Picatout/pomme_1P/KiCAD/pomme-1+/alimentation.kicad_sch

## KiCad design KiCAD/pomme-1+/alimentation.kicad_sch (2025-05-06, an earlier design)

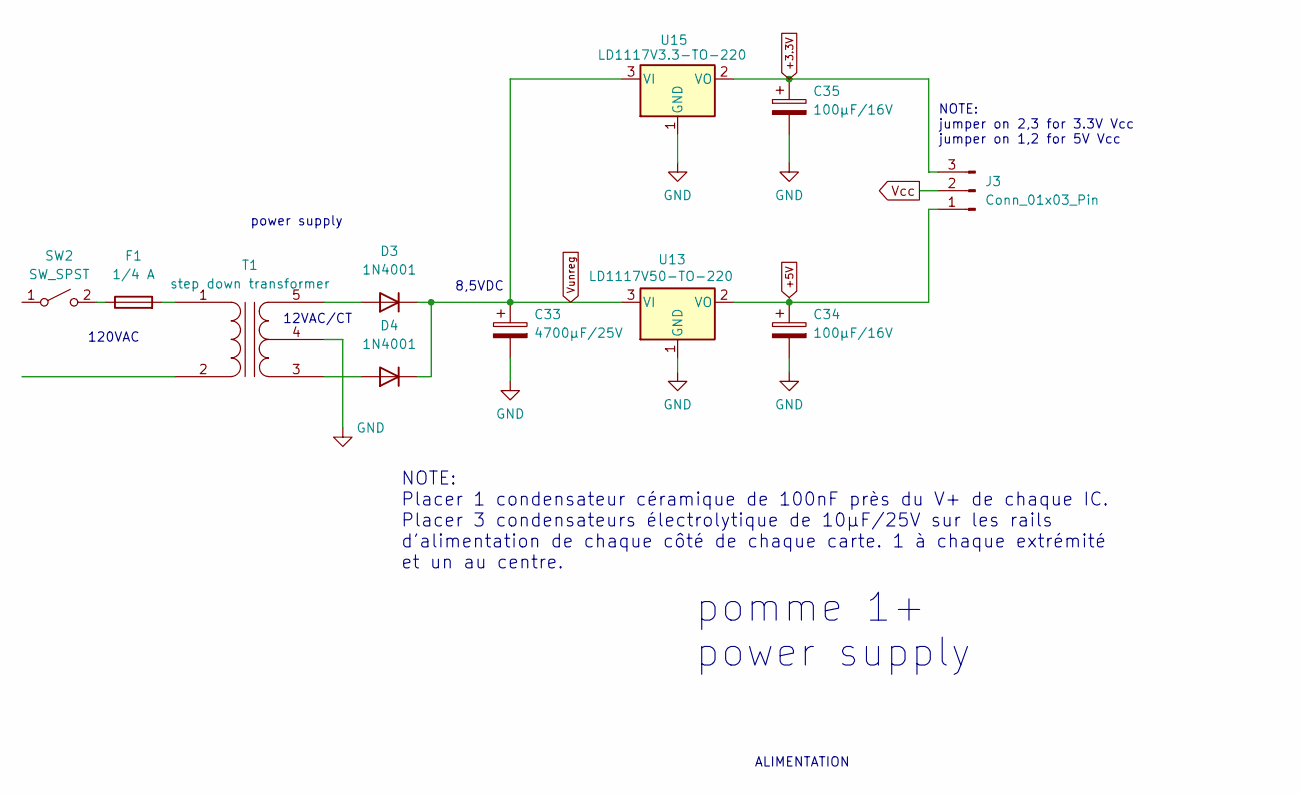
[picture p36: schematic alimentation.kicad_sch]

Parts:
C33: 4700µF/25V
C34, C35: 100µF/16V
D3, D4: 1N4001; D_DO-41_SOD81_P10.16mm_Horizontal
F1: 1/4 A
J3: Conn_01x03_Pin
SW2: SW_SPST
T1: step down transformer
U13: LD1117V50-TO-220; SOT-223-3_TabPin2
U15: LD1117V3.3-TO-220; SOT-223-3_TabPin2

Connections:
+3.3V: C35.1, J3.3, U15.2 (VO)
+5V: C34.1, J3.1, U13.2 (VO)
GND: C33.2, C34.2, C35.2, T1.4 (SC), U13.1 (GND), U15.1 (GND)
unnamed: D3.2 (A), T1.5 (SB)
unnamed: D4.2 (A), T1.3 (SA)
unnamed: F1.1, SW2.2 (B)
unnamed: F1.2, T1.1 (AA)
Vcc: J3.2
Vunreg: C33.1, D3.1 (K), D4.1 (K), U13.3 (VI), U15.3 (VI)

Notes on the sheet:
NOTE: jumper on 2,3 for 3.3V Vcc jumper on 1,2 for 5V Vcc
120VAC
NOTE: Placer 1 condensateur céramique de 100nF près du V+ de chaque IC. Placer 3 condensateurs électrolytique de 10µF/25V sur les rails d'alimentation de chaque côté de chaque carte. 1 à chaque extrémité et un au centre.
pomme 1+ power supply
power supply
12VAC/CT
8,5VDC
ALIMENTATION
