Picatout/pomme_1P/KiCAD/pomme-1+/drive.kicad_sch

## KiCad design KiCAD/pomme-1+/drive.kicad_sch (2025-03-16)

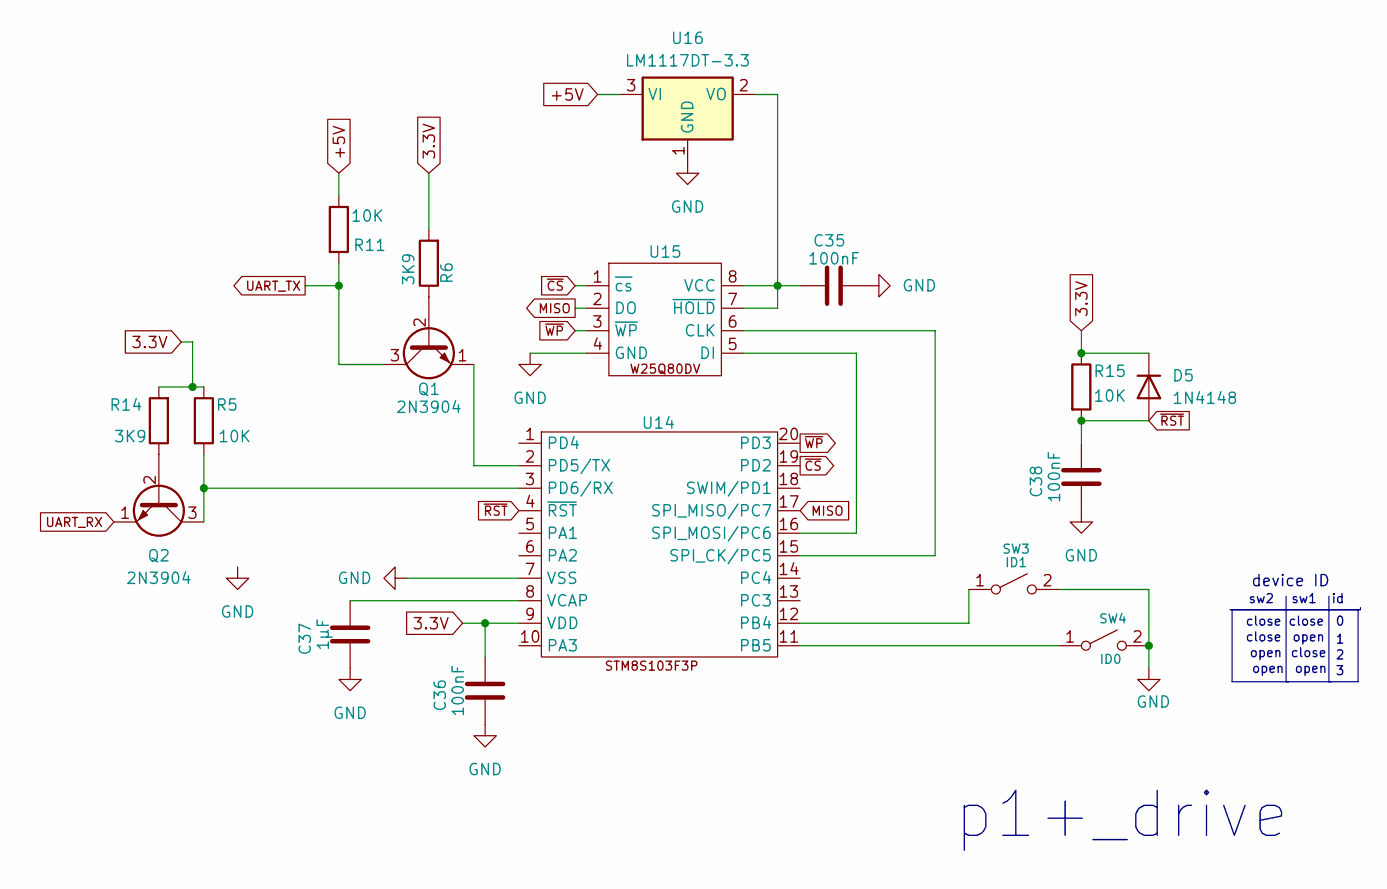
[picture p37: schematic drive.kicad_sch]

Parts:
C35, C36, C38: 100nF
C37: 1µF
D5: 1N4148; D_DO-35_SOD27_P7.62mm_Horizontal
Q1, Q2: 2N3904; TO-92_Inline
R5, R11, R15: 10K
R6, R14: 3K9
SW3: ID1
SW4: ID0
U14, U15: (no value)
U16: LM1117DT-3.3; TO-252-3_TabPin2

Connections:
3.3V: C36.2, D5.1 (K), R5.1, R6.2, R14.2, R15.1, U14.9 (VDD)
+5V: R11.1, U16.3 (VI)
GND: C35.2, C36.1, C37.1, C38.1, SW3.2 (B), SW4.2 (B), U14.7 (VSS), U15.4 (GND), U16.1 (GND)
MISO: U14.17 (SPI_MISO/PC7), U15.2 (DO)
unnamed: C35.1, U15.7 (~HOLD), U15.8 (VCC), U16.2 (VO)
unnamed: C37.2, U14.8 (VCAP)
unnamed: Q1.1 (E), U14.2 (PD5/TX)
unnamed: Q1.2 (B), R6.1
unnamed: Q2.2 (B), R14.1
unnamed: Q2.3 (C), R5.2, U14.3 (PD6/RX)
unnamed: SW3.1 (A), U14.12 (PB4)
unnamed: SW4.1 (A), U14.11 (PB5)
unnamed: U14.15 (SPI_CK/PC5), U15.6 (CLK)
unnamed: U14.16 (SPI_MOSI/PC6), U15.5 (DI)
UART_RX: Q2.1 (E)
UART_TX: Q1.3 (C), R11.2
~CS: U14.19 (PD2), U15.1 (~cs)
~RST: C38.2, D5.2 (A), R15.2, U14.4 (~RST)
~WP: U14.20 (PD3), U15.3 (~WP)

Notes on the sheet:
close
sw1
open
device ID
sw2
p1+_drive
