Picatout/pomme_1P/KiCAD/pomme-1+/mémoire.kicad_sch

## KiCad design KiCAD/pomme-1+/mémoire.kicad_sch (2025-06-10, an earlier design)

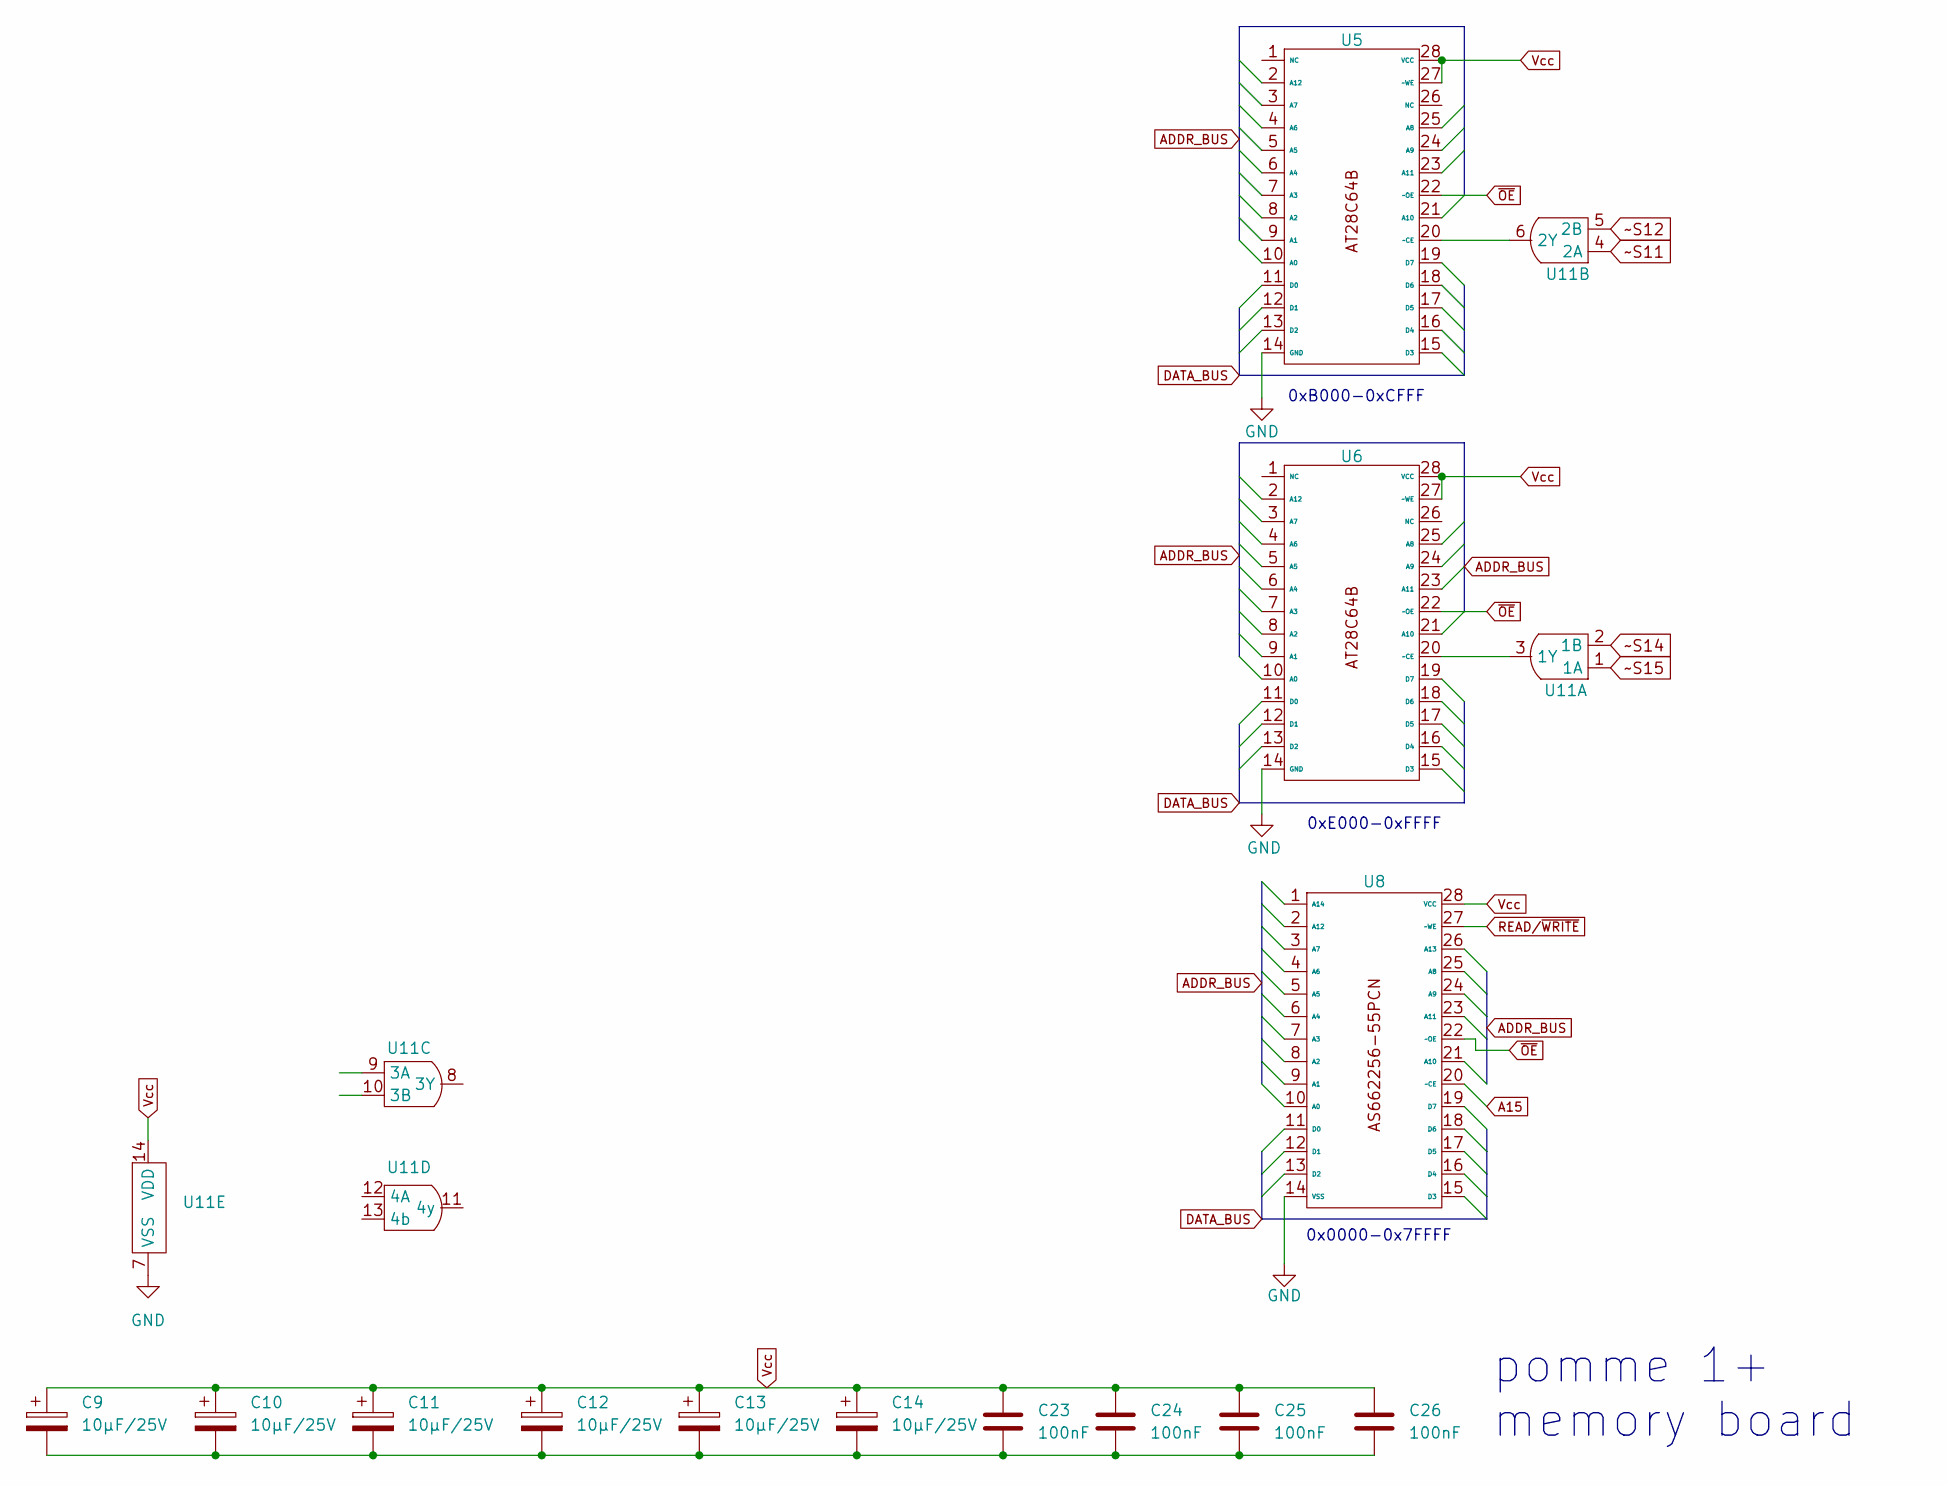
[picture p38: schematic mémoire.kicad_sch]

Parts:
C9, C10, C11, C12, C13, C14: 10µF/25V
C23, C24, C25, C26: 100nF
U5, U6, U8, U11: (no value)

Connections:
GND: U5.14 (GND), U6.14 (GND), U8.14 (VSS), U11.7 (VSS)
unnamed: C9.2, C10.2, C11.2, C12.2, C13.2, C14.2, C23.2, C24.2, C25.2, C26.2
unnamed: U6.20 (~CE), U11.3 (1Y)
unnamed: U5.20 (~CE), U11.6 (2Y)
READ/~WRITE: U8.27 (~WE)
Vcc: C9.1, C10.1, C11.1, C12.1, C13.1, C14.1, C23.1, C24.1, C25.1, C26.1, U5.27 (~WE), U5.28 (VCC), U6.27 (~WE), U6.28 (VCC), U8.28 (VCC), U11.14 (VDD)
~S11: U11.4 (2A)
~S12: U11.5 (2B)
~S14: U11.2 (1B)
~S15: U11.1 (1A)
~OE: U5.22 (~OE), U6.22 (~OE), U8.22 (~OE)

Notes on the sheet:
0x0000-0x7FFFF
0xB000-0xCFFF
pomme 1+ memory board
0xE000-0xFFFF
