Picatout/pomme_1P/KiCAD/pomme-1+/pomme-1.5.kicad_sch

## KiCad design KiCAD/pomme-1+/pomme-1.5.kicad_sch (2025-06-10, an earlier design)

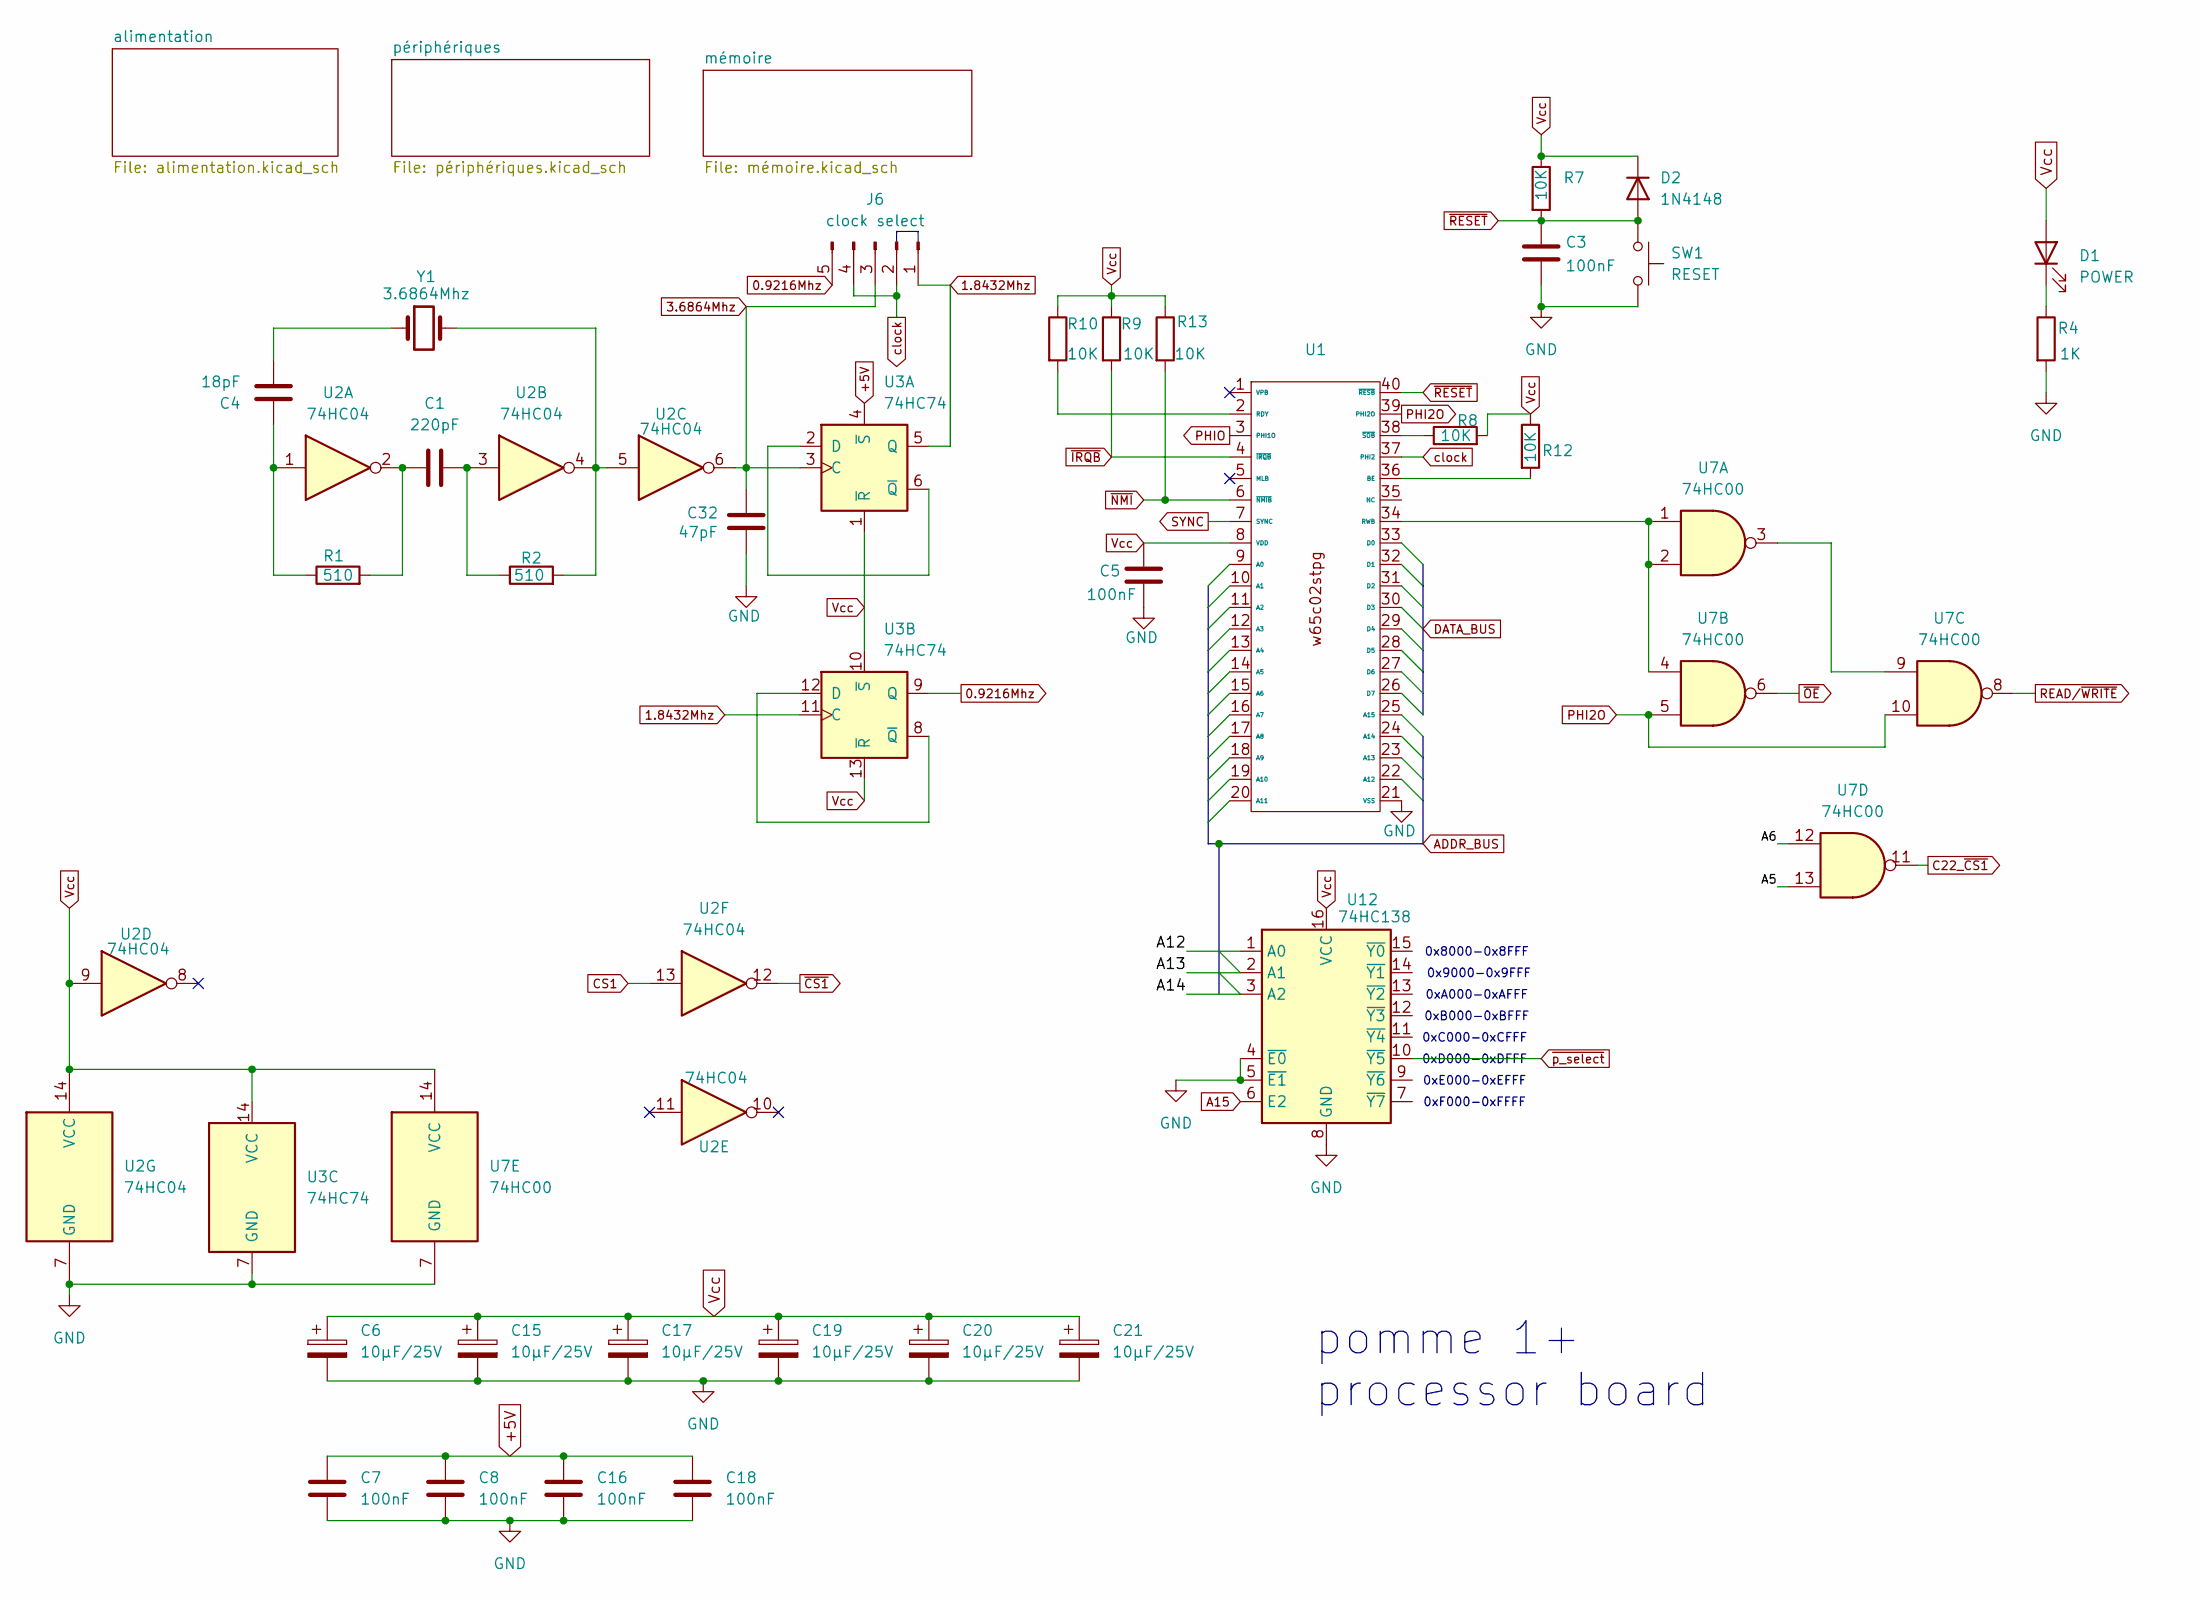
[picture p39: schematic pomme-1.5.kicad_sch]

Parts:
C1: 220pF
C3, C5, C7, C8, C16, C18: 100nF
C4: 18pF
C6, C15, C17, C19, C20, C21: 10µF/25V
C32: 47pF
D1: POWER
D2: 1N4148; D_DO-35_SOD27_P7.62mm_Horizontal
J6: clock select
R1, R2: 510
R4: 1K
R7, R8, R9, R10, R12, R13: 10K
SW1: RESET
U1: (no value)
U2: 74HC04
U3: 74HC74
U7: 74HC00
U12: 74HC138
Y1: 3.6864Mhz

Connections:
0.9216Mhz: J6.5, U3.9 (Q)
1.8432Mhz: J6.1, U3.5 (Q), U3.11 (C)
3.6864Mhz: C32.2, J6.3, U2.6, U3.3 (C)
+5V: C7.1, C8.1, C16.1, C18.1, U3.4 (~S)
A5: U7.13
A6: U7.12
A12: U12.1 (A0)
A13: U12.2 (A1)
A14: U12.3 (A2)
A15: U12.6 (E2)
C22_~CS1: U7.11
CS1: U2.13
GND: C3.2, C5.2, C6.2, C7.2, C8.2, C15.2, C16.2, C17.2, C18.2, C19.2, C20.2, C21.2, C32.1, R4.2, SW1.3 (B), SW1.4 (B), U1.21 (VSS), U2.7 (GND), U3.7 (GND), U7.7 (GND), U12.4 (~E0), U12.5 (~E1), U12.8 (GND)
unnamed: C1.1, R1.2, U2.2
unnamed: C1.2, R2.1, U2.3
unnamed: C4.1, Y1.1
unnamed: C4.2, R1.1, U2.1
unnamed: D1.1 (K), R4.1
unnamed: R2.2, U2.4, U2.5, Y1.2
unnamed: R8.1, U1.38 (~SOB)
unnamed: R10.2, U1.2 (RDY)
unnamed: R12.2, U1.36 (BE)
unnamed: U1.34 (RWB), U7.1, U7.2, U7.4
unnamed: U3.2 (D), U3.6 (~Q)
unnamed: U3.8 (~Q), U3.12 (D)
unnamed: U7.3, U7.9
PHI2O: U1.39 (PHI2O), U7.5, U7.10
PHIO: U1.3 (PHI1O)
READ/~WRITE: U7.8
SYNC: U1.7 (SYNC)
Vcc: C5.1, C6.1, C15.1, C17.1, C19.1, C20.1, C21.1, D1.2 (A), D2.1 (K), R7.1, R8.2, R9.1, R10.1, R12.1, R13.1, U1.8 (VDD), U2.9, U2.14 (VCC), U3.1 (~R), U3.10 (~S), U3.13 (~R), U3.14 (VCC), U7.14 (VCC), U12.16 (VCC)
clock: J6.2, J6.4, U1.37 (PHI2)
~CS1: U2.12
~IRQB: R9.2, U1.4 (~IRQB)
~NMI: R13.2, U1.6 (~NMIB)
~OE: U7.6
~RESET: C3.1, D2.2 (A), R7.2, SW1.1 (A), SW1.2 (A), U1.40 (~RESB)
~p_select: U12.10 (~Y5)

Notes on the sheet:
0x9000-0x9FFF
pomme 1+ processor board
0xF000-0xFFFF
0xE000-0xEFFF
0xD000-0xDFFF
0xA000-0xAFFF
0xB000-0xBFFF
0x8000-0x8FFF
0xC000-0xCFFF
