Picatout/pomme_1P/KiCAD/pomme-1+/périphériques.kicad_sch

## KiCad design KiCAD/pomme-1+/périphériques.kicad_sch (2025-06-10, an earlier design)

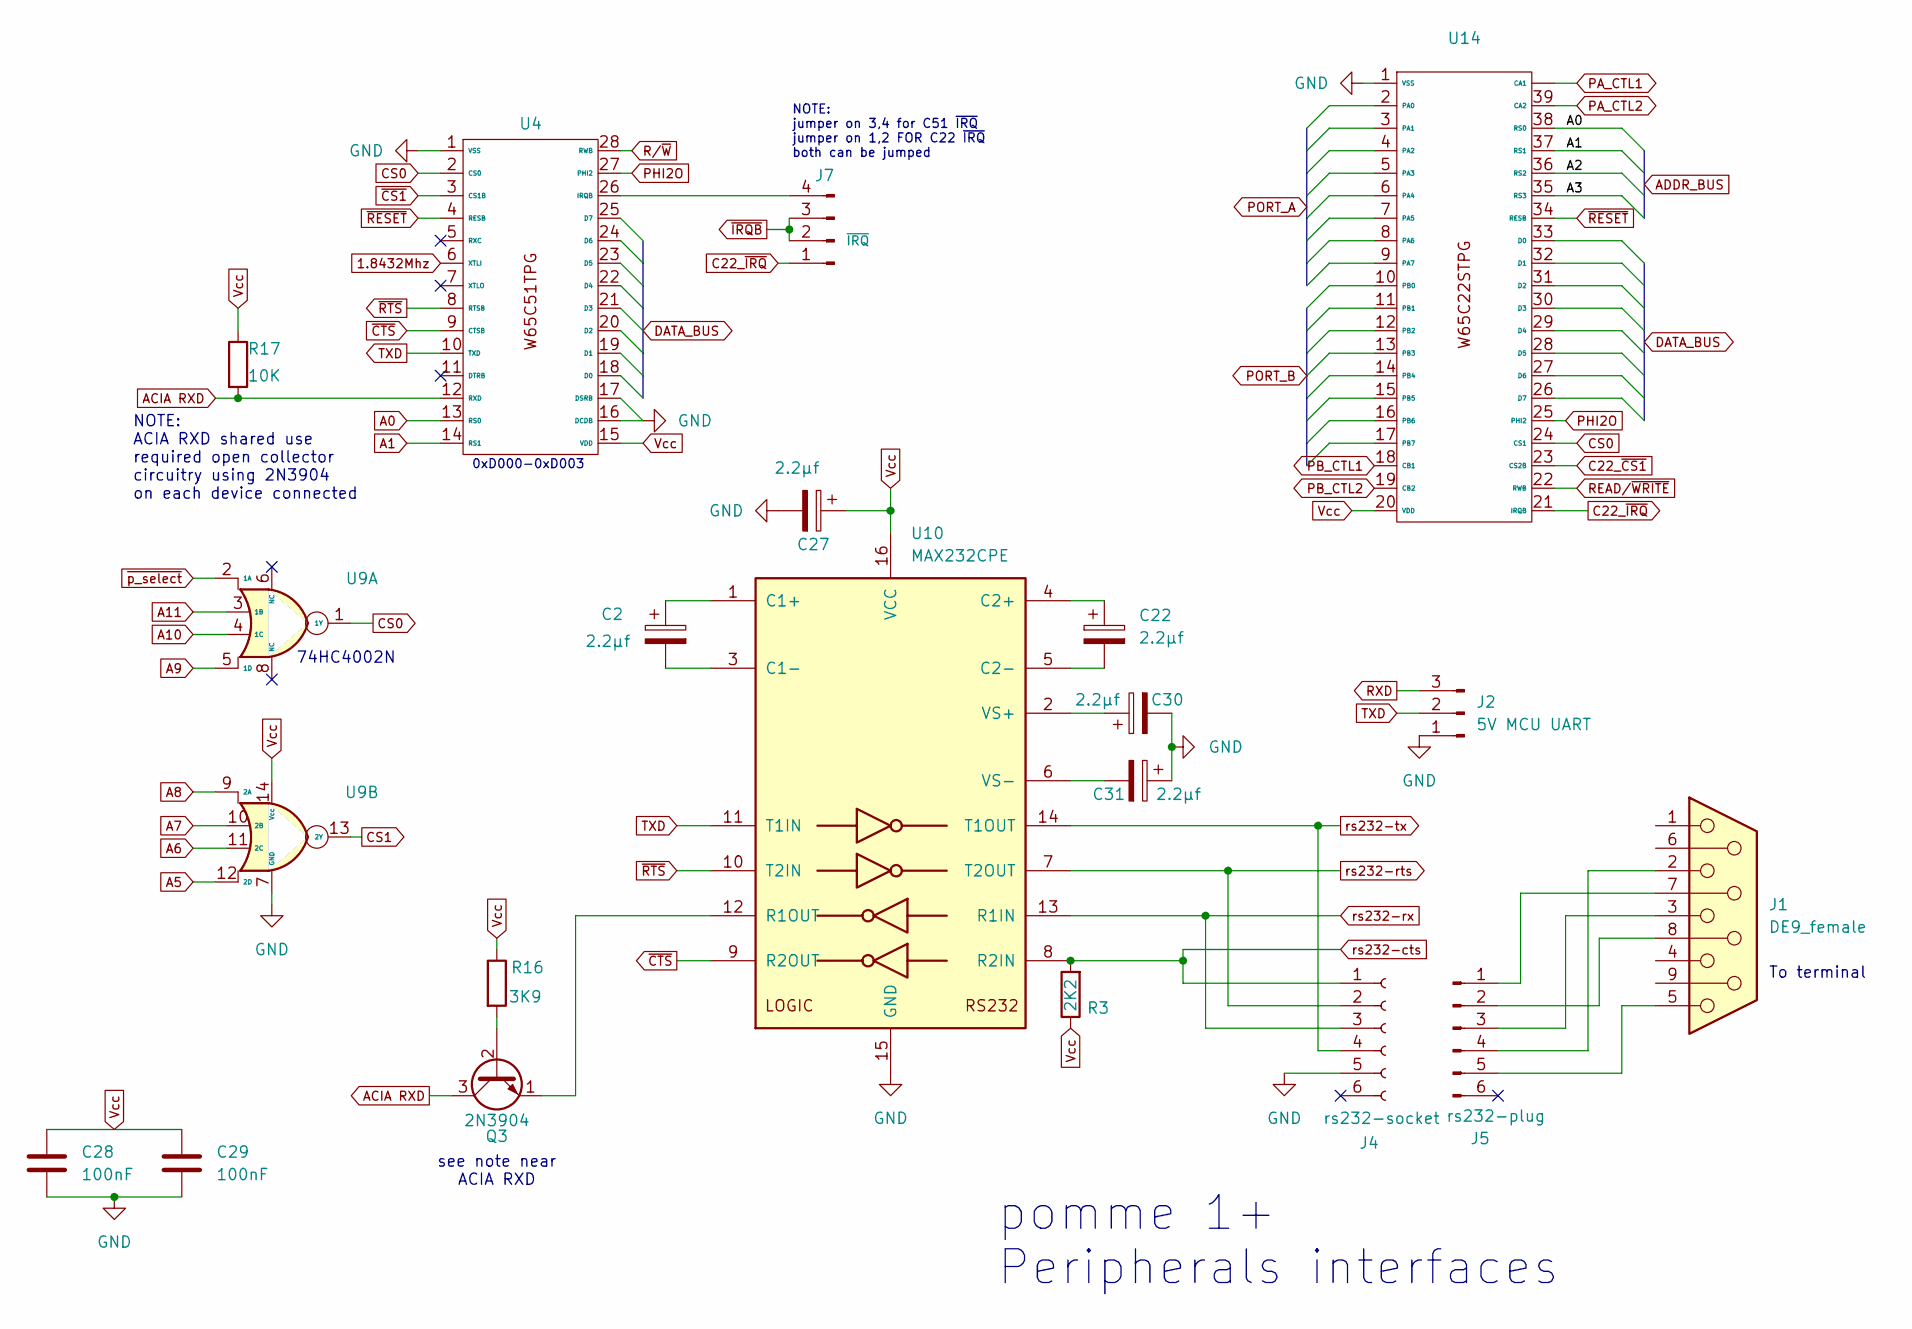
[picture p40: schematic périphériques.kicad_sch]

Parts:
C2, C22, C27, C30, C31: 2.2µf
C28, C29: 100nF
J1: DE9_female
J2: 5V MCU UART
J4: rs232-socket
J5: rs232-plug
J7: ~{IRQ}
Q3: 2N3904; TO-92_Inline
R3: 2K2
R16: 3K9
R17: 10K
U4, U9, U14: (no value)
U10: MAX232CPE

Connections:
1.8432Mhz: U4.6 (XTLI)
A0: U4.13 (RS0), U14.38 (RS0)
A1: U4.14 (RS1), U14.37 (RS1)
A2: U14.36 (RS2)
A3: U14.35 (RS3)
A5: U9.12 (2D)
A6: U9.11 (2C)
A7: U9.10 (2B)
A8: U9.9 (2A)
A9: U9.5 (1D)
A10: U9.4 (1C)
A11: U9.3 (1B)
ACIA RXD: Q3.3 (C), R17.2, U4.12 (RXD)
C22_~CS1: U14.23 (CS2B)
C22_~IRQ: J7.1, U14.21 (IRQB)
CS0: U4.2 (CS0), U9.1 (1Y), U14.24 (CS1)
CS1: U9.13 (2Y)
GND: C27.2, C28.1, C29.2, C30.2, C31.1, J2.1, J4.5, U4.1 (VSS), U4.16 (DCDB), U9.7 (GND), U10.15 (GND), U14.1 (VSS)
unnamed: C2.1, U10.1 (C1+)
unnamed: C2.2, U10.3 (C1-)
unnamed: C22.1, U10.4 (C2+)
unnamed: C22.2, U10.5 (C2-)
unnamed: C30.1, U10.2 (VS+)
unnamed: C31.2, U10.6 (VS-)
unnamed: J1.2, J5.4
unnamed: J1.3, J5.3
unnamed: J1.5, J5.5
unnamed: J1.7, J5.1
unnamed: J1.8, J5.2
unnamed: J7.4, U4.26 (IRQB)
unnamed: Q3.1 (E), U10.12 (R1OUT)
unnamed: Q3.2 (B), R16.2
PA_CTL1: U14. (CA1)
PA_CTL2: U14.39 (CA2)
PB_CTL1: U14.18 (CB1)
PB_CTL2: U14.19 (CB2)
PHI2O: U4.27 (PHI2), U14.25 (PHI2)
READ/~WRITE: U14.22 (RWB)
RXD: J2.3
R/~W: U4.28 (RWB)
TXD: J2.2, U4.10 (TXD), U10.11 (T1IN)
Vcc: C27.1, C28.2, C29.1, R3.1, R16.1, R17.1, U4.15 (VDD), U9.14 (Vcc), U10.16 (VCC), U14.20 (VDD)
rs232-cts: J4.1, R3.2, U10.8 (R2IN)
rs232-rts: J4.2, U10.7 (T2OUT)
rs232-rx: J4.3, U10.13 (R1IN)
rs232-tx: J4.4, U10.14 (T1OUT)
~CS1: U4.3 (CS1B)
~CTS: U4.9 (CTSB), U10.9 (R2OUT)
~IRQB: J7.2, J7.3
~RESET: U4.4 (RESB), U14.34 (RESB)
~RTS: U4.8 (RTSB), U10.10 (T2IN)
~p_select: U9.2 (1A)

Notes on the sheet:
see note near ACIA RXD
To terminal
NOTE: jumper on 3,4 for C51 ~{IRQ} jumper on 1,2 FOR C22 ~{IRQ} both can be jumped
74HC4002N
0xD000-0xD003
NOTE: ACIA RXD shared use required open collector circuitry using 2N3904 on each device connected
pomme 1+ Peripherals interfaces
