Picatout/pomme_1P/p1+_drive/KiCAD/p1+_drive.kicad_sch

## KiCad design p1+_drive/KiCAD/p1+_drive.kicad_sch (2025-04-16)

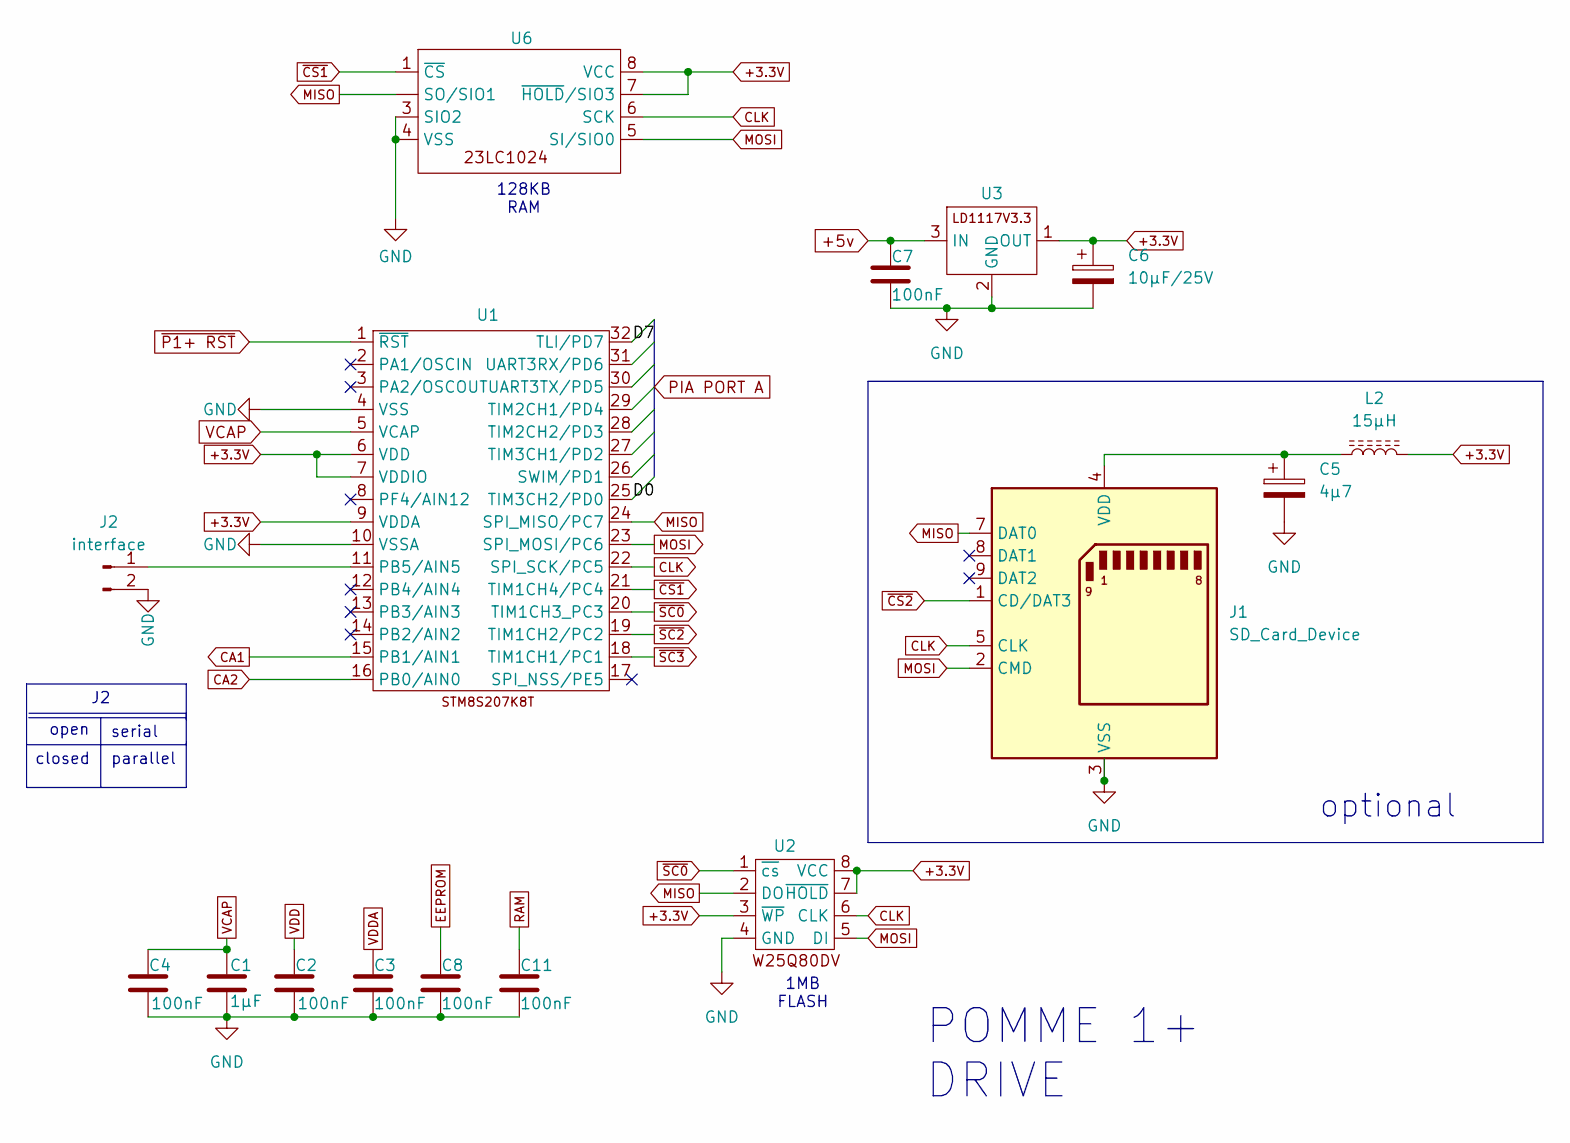
[picture p42: schematic p1+_drive.kicad_sch]

Parts:
C1: 1µF
C2, C3, C4, C7, C8, C11: 100nF
C5: 4µ7
C6: 10µF/25V
J1: SD_Card_Device
J2: interface
L2: 15µH
U1, U2, U3, U6: (no value)

Connections:
+3.3V: C6.1, L2.2, U1.6 (VDD), U1.7 (VDDIO), U1.9 (VDDA), U2.3 (~WP), U2.7 (~HOLD), U2.8 (VCC), U3.1 (OUT), U6.7 (~HOLD/SIO3), U6.8 (VCC)
+5v: C7.1, U3.3 (IN)
CA1: U1.15 (PB1/AIN1)
CA2: U1.16 (PB0/AIN0)
CLK: J1.5 (CLK), U1.22 (SPI_SCK/PC5), U2.6 (CLK), U6.6 (SCK)
D0: U1.25 (TIM3CH2/PD0)
D7: U1.32 (TLI/PD7)
EEPROM: C8.1
GND: C1.2, C2.2, C3.2, C4.2, C5.2, C6.2, C7.2, C8.2, C11.2, J1.3 (VSS), J1.6 (VSS), J2.2, U1.4 (VSS), U1.10 (VSSA), U2.4 (GND), U3.2 (GND), U6.3 (SIO2), U6.4 (VSS)
MISO: J1.7 (DAT0), U1.24 (SPI_MISO/PC7), U2.2 (DO), U6. (SO/SIO1)
MOSI: J1.2 (CMD), U1.23 (SPI_MOSI/PC6), U2.5 (DI), U6.5 (SI/SIO0)
unnamed: C5.1, J1.4 (VDD), L2.1
unnamed: J2.1, U1.11 (PB5/AIN5)
RAM: C11.1
VCAP: C1.1, C4.1, U1.5 (VCAP)
VDD: C2.1
VDDA: C3.1
~CS1: U1.21 (TIM1CH4/PC4), U6.1 (~CS)
~CS2: J1.1 (CD/DAT3)
~P1+ RST: U1.1 (~RST)
~SC0: U1.20 (TIM1CH3_PC3), U2.1 (~cs)
~SC2: U1.19 (TIM1CH2/PC2)
~SC3: U1.18 (TIM1CH1/PC1)

Notes on the sheet:
parallel
POMME 1+ DRIVE
open
optional
1MB FLASH
128KB RAM
serial
closed
