Picatout/pomme_1P/p1+_drive/KiCAD/stm8l151.kicad_sch

## KiCad design p1+_drive/KiCAD/stm8l151.kicad_sch (2025-04-09)

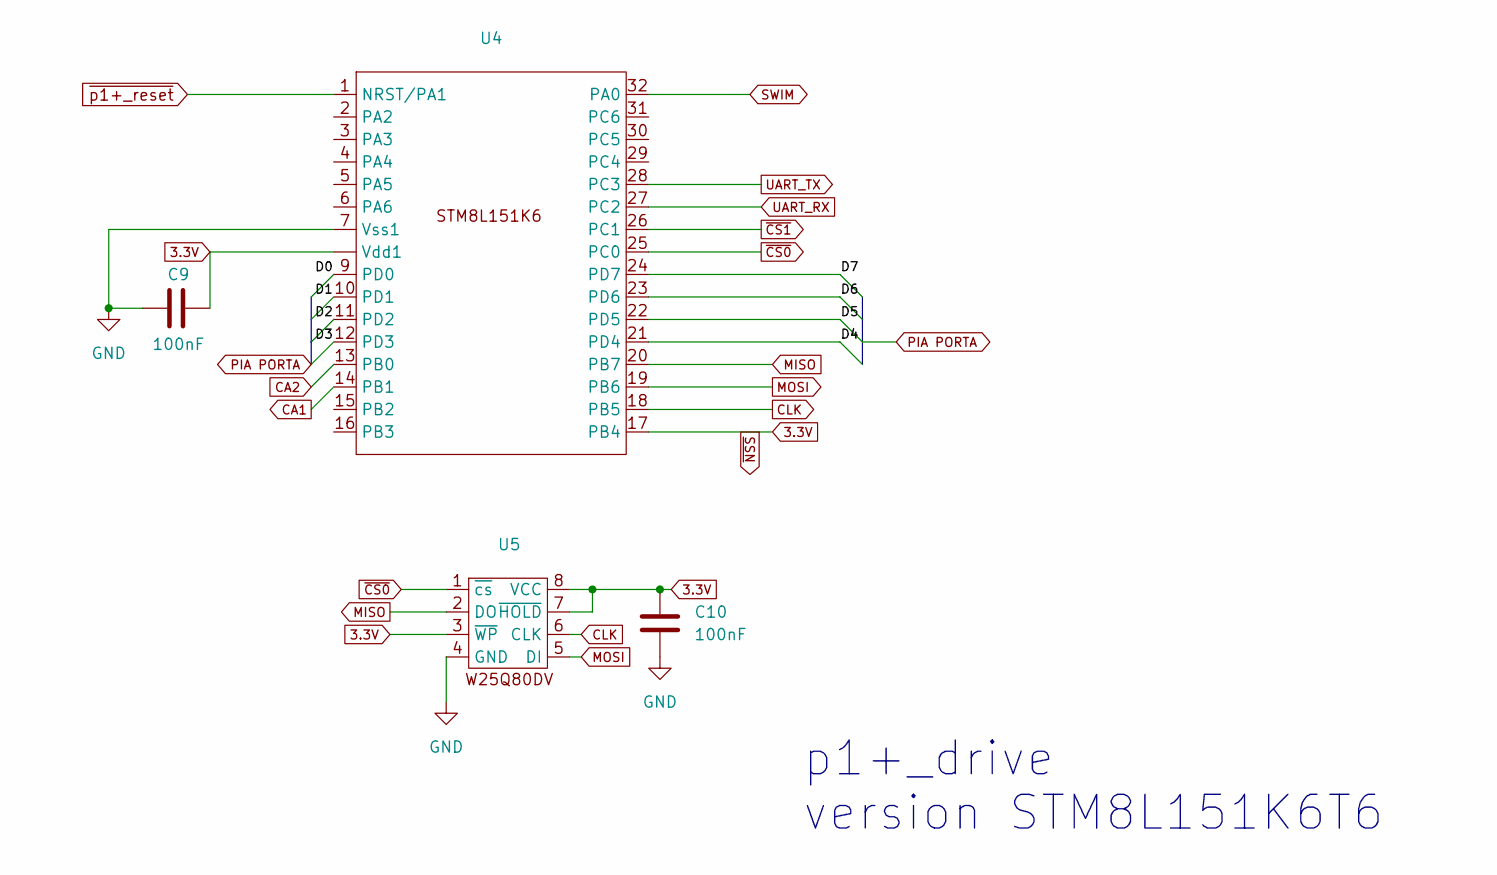
[picture p43: schematic stm8l151.kicad_sch]

Parts:
C9, C10: 100nF
U4, U5: (no value)

Connections:
3.3V: C9.2, C10.1, U4. (Vdd1), U4.17 (PB4), U5.3 (~WP), U5.7 (~HOLD), U5.8 (VCC)
CLK: U4.18 (PB5), U5.6 (CLK)
D0: U4.9 (PD0)
D1: U4.10 (PD1)
D2: U4.11 (PD2)
D3: U4.12 (PD3)
D4: U4.21 (PD4)
D5: U4.22 (PD5)
D6: U4.23 (PD6)
D7: U4.24 (PD7)
GND: C9.1, C10.2, U4.7 (Vss1), U5.4 (GND)
MISO: U4.20 (PB7), U5.2 (DO)
MOSI: U4.19 (PB6), U5.5 (DI)
SWIM: U4.32 (PA0)
UART_RX: U4.27 (PC2)
UART_TX: U4.28 (PC3)
~CS0: U4.25 (PC0), U5.1 (~cs)
~CS1: U4.26 (PC1)
~p1+_reset: U4.1 (NRST/PA1)

Notes on the sheet:
p1+_drive version STM8L151K6T6
