Picatout/pomme_1P/docs/montage révison 2(2).jpg

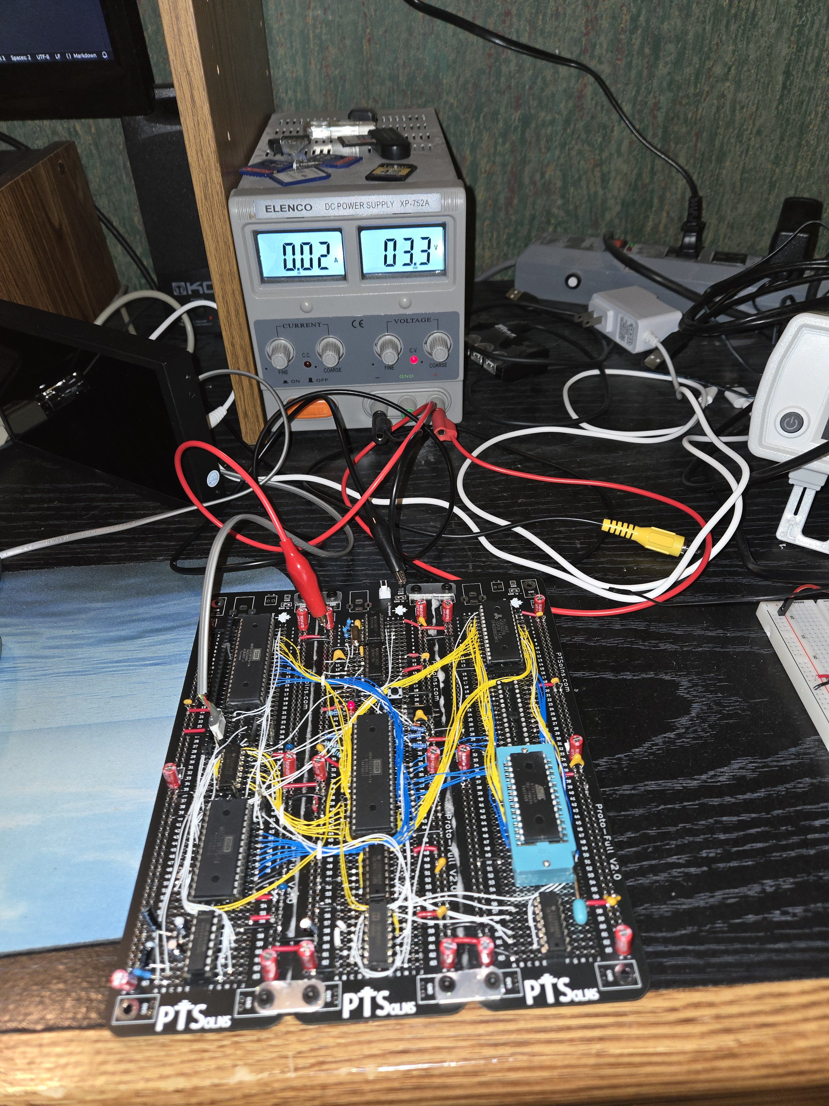
docs/montage révison 2(2).jpg
